dchristie75/SSD1306-Monochrome-OLED/Index_src/20181113_000239.jpg

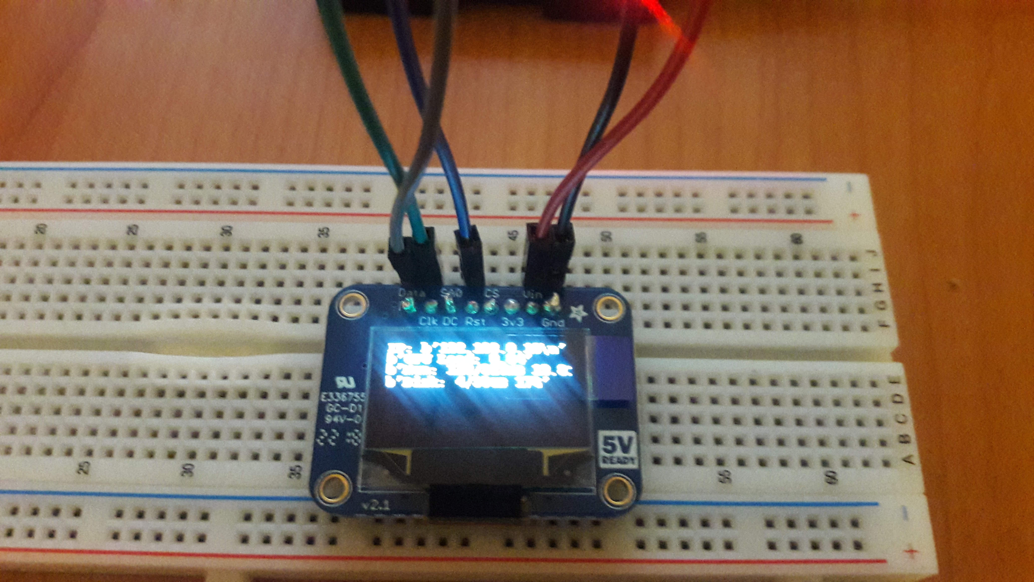
Index_src/20181113_000239.jpg
