dchristie75/SSD1306-Monochrome-OLED/Index_src/pcbwithheaders1.jpg

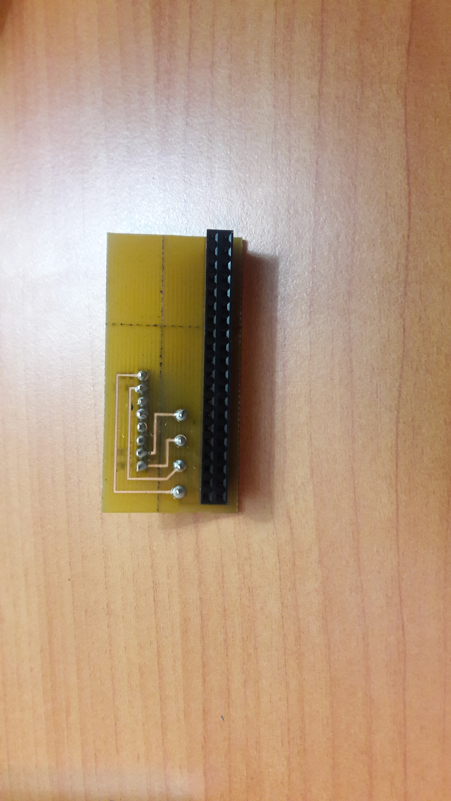
Index_src/pcbwithheaders1.jpg
