dchristie75/SSD1306-Monochrome-OLED/Index_src/pcbwithheaders2.jpg

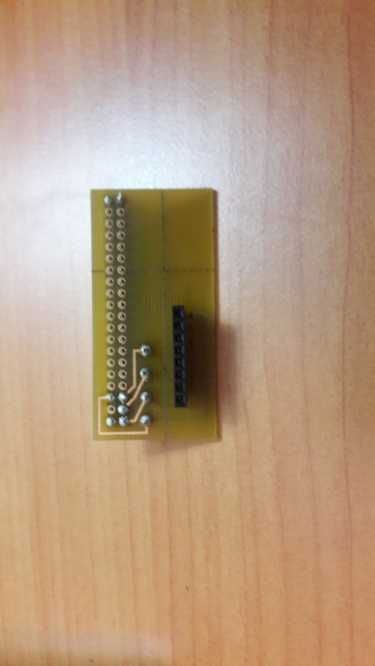
Index_src/pcbwithheaders2.jpg
