dchristie75/SSD1306-Monochrome-OLED/Index_src/stackable1.jpg

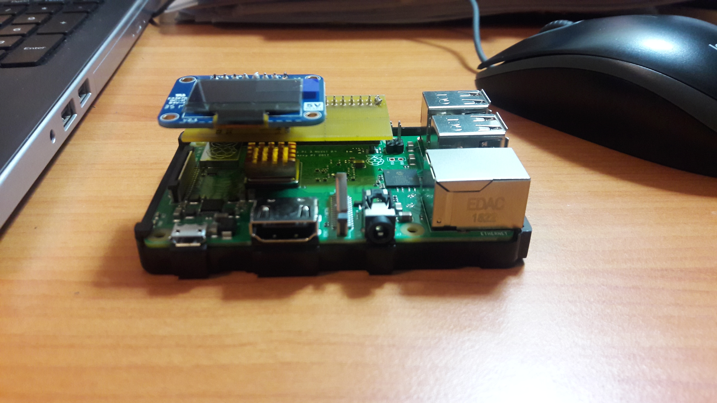
Index_src/stackable1.jpg
