dchristie75/SSD1306-Monochrome-OLED/Index_src/stackable2.jpg

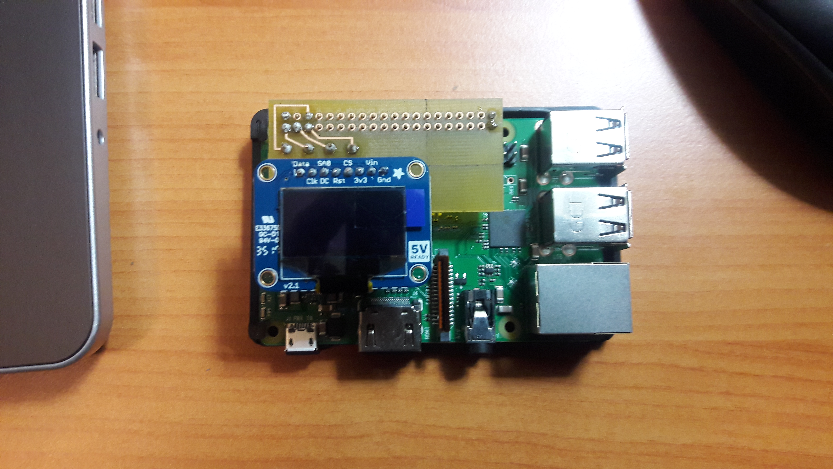
Index_src/stackable2.jpg
